adamlechowicz/Beton3/Picture Gallery/0001.jpeg

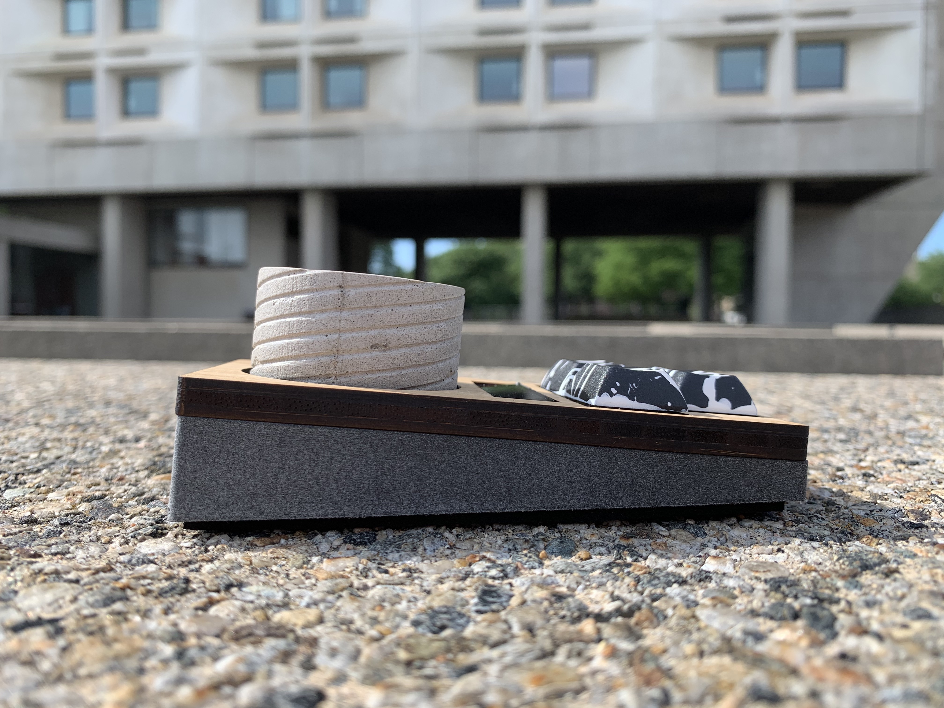
Picture Gallery/0001.jpeg
