adamlechowicz/Beton3/Picture Gallery/0005.jpeg

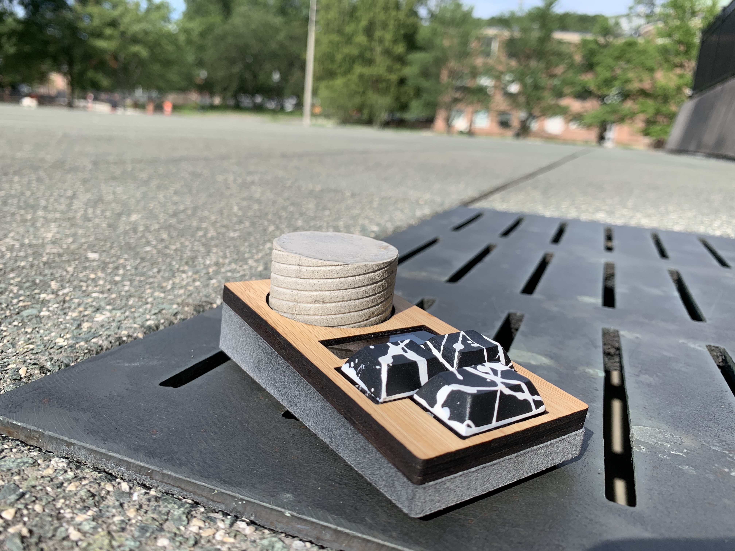
Picture Gallery/0005.jpeg
