adamlechowicz/Beton3/Picture Gallery/0007.jpeg

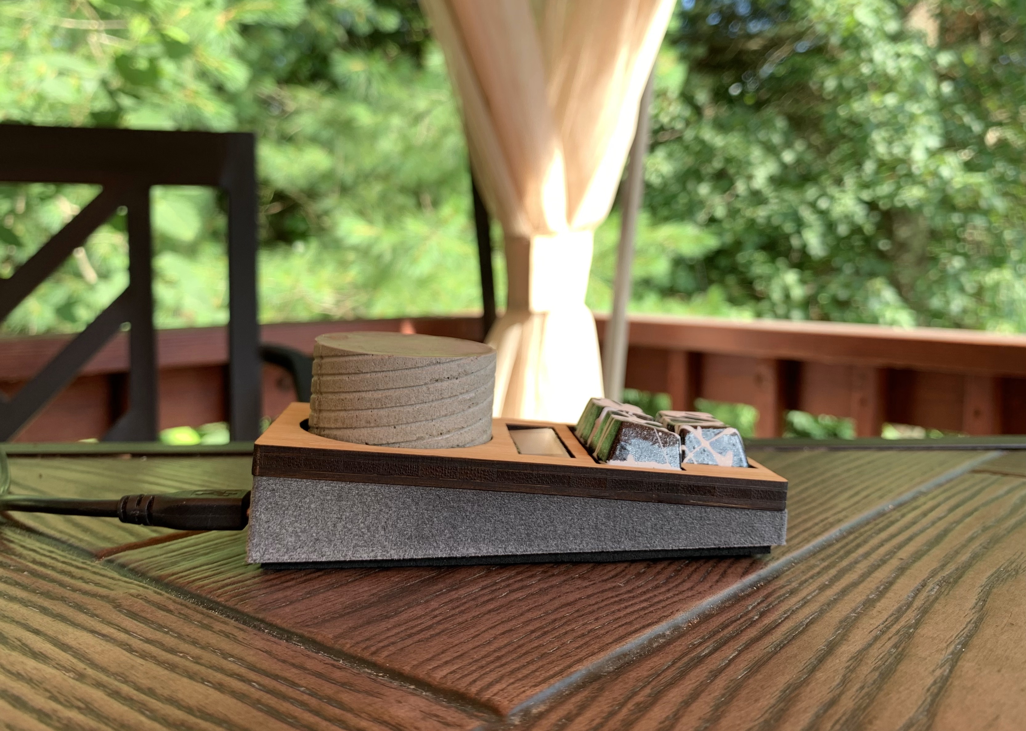
Picture Gallery/0007.jpeg
