adamlechowicz/Beton3/Picture Gallery/0008.jpeg

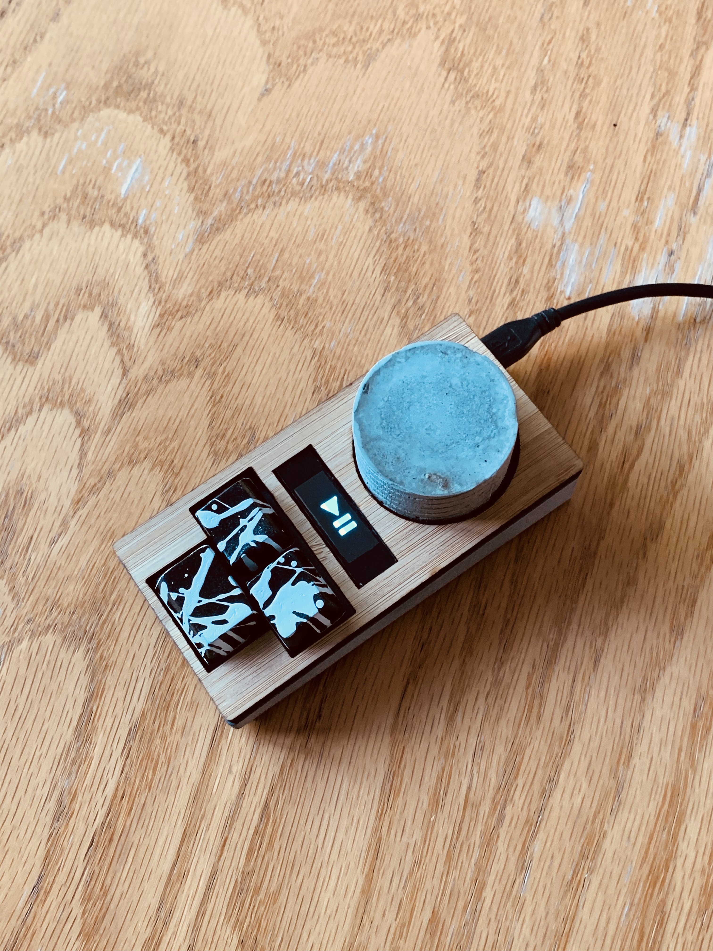
Picture Gallery/0008.jpeg
