adamlechowicz/Beton3/Firmware Source Files/beton_firmware1.1/beton/play.h

//# of pixels for a standard icon
#define icon_width 32
#define icon_height 32

//XBM format play icon
static const unsigned char play[] U8X8_PROGMEM = {
 0x00,0x00,0x00,0x00,0x00,0x00,0x00,0x00,0x18,0x00,0x00,0x00,0x7c,0x00,0x00,
 0x00,0xfc,0x01,0x00,0x00,0xfc,0x07,0x00,0x00,0xfc,0x1f,0x00,0x00,0xfc,0x7f,
 0x00,0x00,0xfc,0xff,0x01,0x00,0xfc,0xff,0x07,0x00,0xfc,0xff,0x1f,0x00,0xfc,
 0xff,0x7f,0x00,0xfc,0xff,0xff,0x01,0xfc,0xff,0xff,0x07,0xfc,0xff,0xff,0x1f,
 0xfc,0xff,0xff,0x3f,0xfc,0xff,0xff,0x3f,0xfc,0xff,0xff,0x1f,0xfc,0xff,0xff,
 0x07,0xfc,0xff,0xff,0x01,0xfc,0xff,0x7f,0x00,0xfc,0xff,0x1f,0x00,0xfc,0xff,
 0x07,0x00,0xfc,0xff,0x01,0x00,0xfc,0x7f,0x00,0x00,0xfc,0x1f,0x00,0x00,0xfc,
 0x07,0x00,0x00,0xfc,0x01,0x00,0x00,0x7c,0x00,0x00,0x00,0x18,0x00,0x00,0x00,
 0x00,0x00,0x00,0x00,0x00,0x00,0x00,0x00 };

//XBM format pause icon
static const unsigned char pause[] U8X8_PROGMEM = {
 0x00,0x00,0x00,0x00,0x00,0x00,0x00,0x00,0xe0,0x0f,0xf0,0x07,0xf0,0x1f,0xf8,
 0x0f,0xf0,0x1f,0xf8,0x0f,0xf0,0x1f,0xf8,0x0f,0xf0,0x1f,0xf8,0x0f,0xf0,0x1f,
 0xf8,0x0f,0xf0,0x1f,0xf8,0x0f,0xf0,0x1f,0xf8,0x0f,0xf0,0x1f,0xf8,0x0f,0xf0,
 0x1f,0xf8,0x0f,0xf0,0x1f,0xf8,0x0f,0xf0,0x1f,0xf8,0x0f,0xf0,0x1f,0xf8,0x0f,
 0xf0,0x1f,0xf8,0x0f,0xf0,0x1f,0xf8,0x0f,0xf0,0x1f,0xf8,0x0f,0xf0,0x1f,0xf8,
 0x0f,0xf0,0x1f,0xf8,0x0f,0xf0,0x1f,0xf8,0x0f,0xf0,0x1f,0xf8,0x0f,0xf0,0x1f,
 0xf8,0x0f,0xf0,0x1f,0xf8,0x0f,0xf0,0x1f,0xf8,0x0f,0xf0,0x1f,0xf8,0x0f,0xf0,
 0x1f,0xf8,0x0f,0xf0,0x1f,0xf8,0x0f,0xf0,0x1f,0xf8,0x0f,0xe0,0x0f,0xf0,0x07,
 0x00,0x00,0x00,0x00,0x00,0x00,0x00,0x00 };

 void drawPlay() {
  u8g2.firstPage();  do {
    switch (animation_state) {
      //this switch statement decides which frame of the animation to draw based on the number in animation_state.
      case 0 ... 10:
        u8g2.setContrast(0);
        u8g2.drawXBMP(12+(animation_state*2), -30+(animation_state*3), icon_width, icon_height, play);
        u8g2.drawXBMP(84-(animation_state*2), 30-(animation_state*3), icon_width, icon_height, pause);
        break;
      case 11 ... 20:
        u8g2.setContrast(255);
        u8g2.drawXBMP(32, 0, icon_width, icon_height, play);
        u8g2.drawXBMP(64, 0, icon_width, icon_height, pause);
        break;
      case 21 ... 31:
        u8g2.setContrast(0);
        u8g2.drawXBMP(74-(animation_state*2), (animation_state*3)-63, icon_width, icon_height, play);
        u8g2.drawXBMP(22+(animation_state*2), -(animation_state*3)+63, icon_width, icon_height, pause);
        break;
      case 32:
        animation = 0;
        break;
    }
  } while ( u8g2.nextPage() );
}
