adamlechowicz/Beton3/Picture Gallery/0003.jpeg

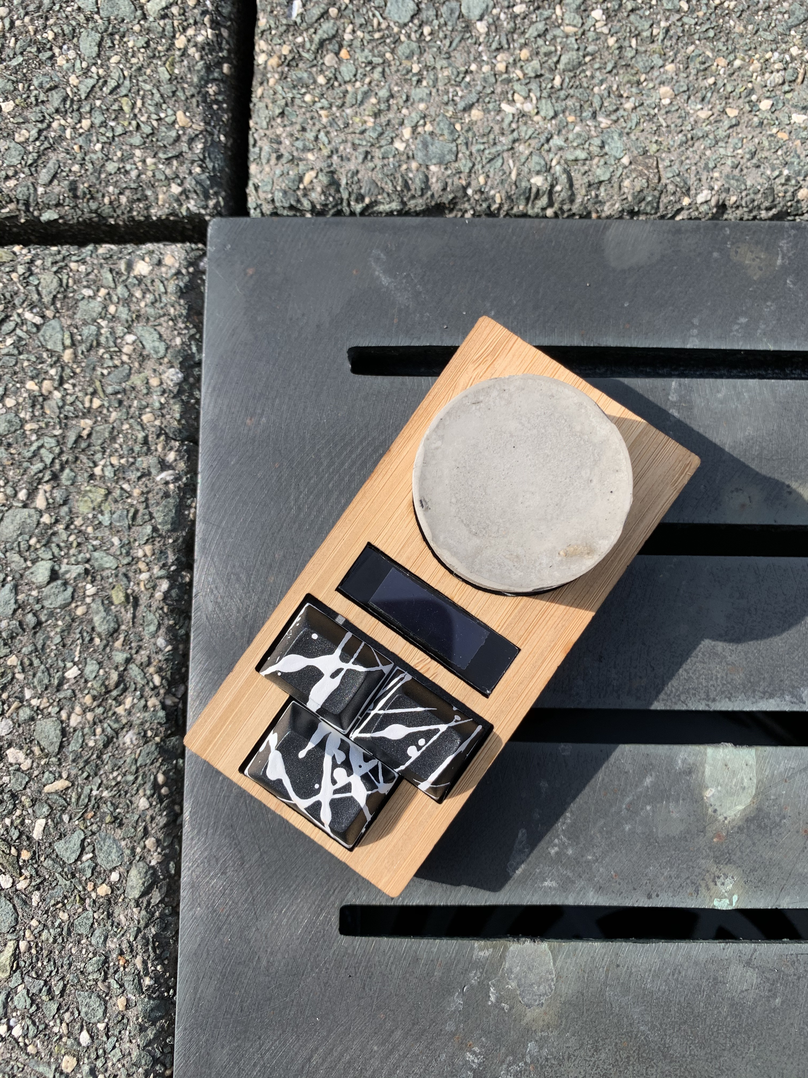
Picture Gallery/0003.jpeg
