adamlechowicz/Beton3/Picture Gallery/0004.jpeg

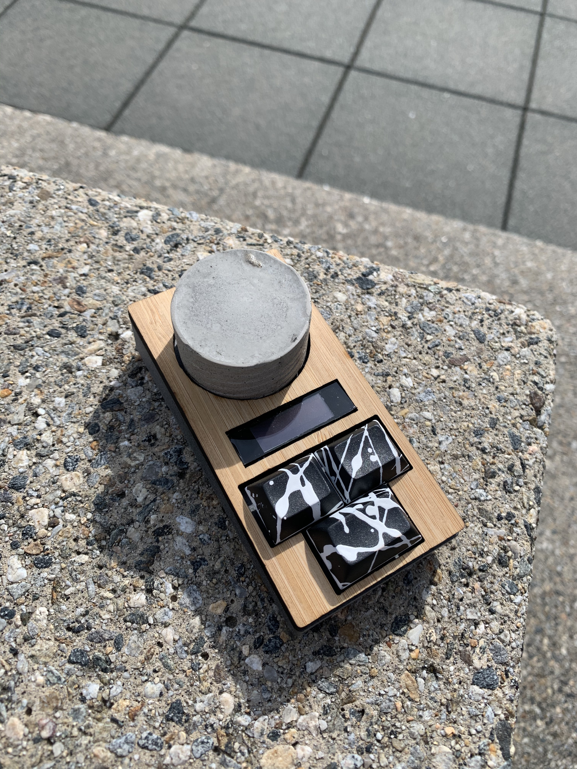
Picture Gallery/0004.jpeg
