adamlechowicz/Beton3/Picture Gallery/0006.jpeg

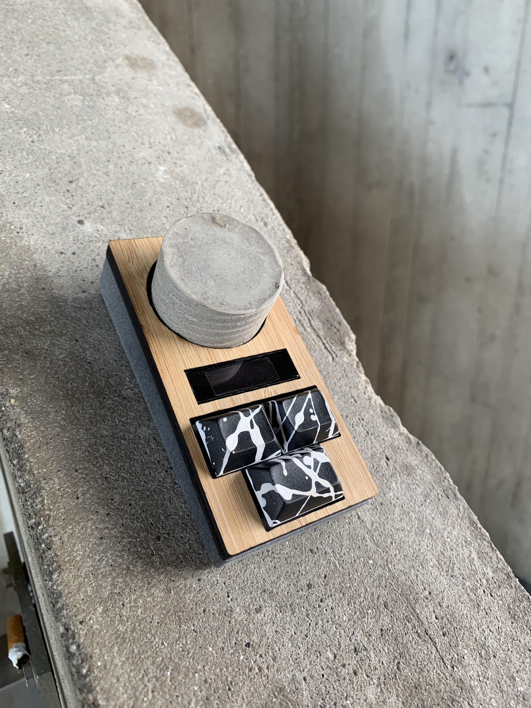
Picture Gallery/0006.jpeg
